fbeckman/SensorCommunications/ESPNowLoRaGateway/include/Credentials.h

#ifndef CREDENTIALS_H
#define CREDENTIALS_H

// WiFi parameters
const char* ssid1 = "YOUR SSID1";
const char* password1 = "YOUR WIFI PASSWORD1";

const char* ssid2 = "YOUR SSID2";
const char* password1 = "YOUR WIFI PASSWORD2";

#define INFLUXDB_HOST "YOUR INFLUXDB HOST IP ADDRESS"

#endif
